bdring/TWANG32/TWANG32/SoundData.h

unsigned char PROGMEM sndStart[14444] = {
  0x52, 0x49, 0x46, 0x46, 0x64, 0x38, 0x00, 0x00, 0x57, 0x41, 0x56, 0x45,
  0x66, 0x6D, 0x74, 0x20, 0x10, 0x00, 0x00, 0x00, 0x01, 0x00, 0x01, 0x00,
  0x40, 0x1F, 0x00, 0x00, 0x40, 0x1F, 0x00, 0x00, 0x01, 0x00, 0x08, 0x00,
  0x64, 0x61, 0x74, 0x61, 0x40, 0x38, 0x00, 0x00, 0x80, 0x80, 0x80, 0x80,
  0x80, 0x7F, 0x80, 0x7F, 0x80, 0x80, 0x7F, 0x80, 0x7F, 0x80, 0x80, 0x7F,
  0x80, 0x7F, 0x80, 0x80, 0x7F, 0x80, 0x7F, 0x80, 0x7F, 0x80, 0x7F, 0x80,
  0x7F, 0x80, 0x7F, 0x80, 0x7F, 0x80, 0x7F, 0x80, 0x7F, 0x80, 0x80, 0x7F,
  0x80, 0x7F, 0x80, 0x80, 0x7F, 0x80, 0x7F, 0x80, 0x80, 0x7F, 0x80, 0x7F,
  0x80, 0x7F, 0x80, 0x80, 0x7F, 0x80, 0x7F, 0x80, 0x7F, 0x80, 0x80, 0x80,
  0x80, 0x80, 0x80, 0x80, 0x80, 0x7F, 0x7F, 0x7F, 0x7F, 0x7F, 0x7F, 0x7F,
  0x7F, 0x7F, 0x7F, 0x7F, 0x7F, 0x7F, 0x80, 0x7F, 0x80, 0x7F, 0x80, 0x80,
  0x80, 0x80, 0x80, 0x80, 0x80, 0x7F, 0x7F, 0x7F, 0x7F, 0x7F, 0x7F, 0x80,
  0x80, 0x80, 0x80, 0x80, 0x80, 0x80, 0x80, 0x80, 0x80, 0x80, 0x80, 0x80,
  0x80, 0x80, 0x80, 0x80, 0x80, 0x80, 0x7F, 0x80, 0x7F, 0x80, 0x7F, 0x80,
  0x80, 0x80, 0x80, 0x80, 0x80, 0x7F, 0x7F, 0x7F, 0x7F, 0x7F, 0x7F, 0x7F,
  0x7F, 0x7F, 0x7F, 0x7F, 0x7F, 0x7F, 0x7F, 0x7F, 0x7F, 0x7F, 0x7F, 0x7F,
  0x80, 0x7F, 0x80, 0x7F, 0x80, 0x7F, 0x7F, 0x7F, 0x7F, 0x7F, 0x7F, 0x80,
  0x80, 0x80, 0x80, 0x80, 0x80, 0x80, 0x80, 0x80, 0x80, 0x80, 0x80, 0x80,
  0x80, 0x80, 0x80, 0x80, 0x80, 0x80, 0x7F, 0x7F, 0x7F, 0x7F, 0x80, 0x80,
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
  0x88, 0x89, 0x89, 0x89, 0x8A, 0x8A, 0x8B, 0x8B, 0x8B, 0x8B, 0x8C, 0x8C,
  0x8D, 0x8D, 0x8E, 0x8D, 0x8E, 0x8E, 0x8F, 0x8F, 0x90, 0x8F, 0x91, 0x90,
  0x92, 0x90, 0x93, 0x90, 0x96, 0x7D, 0x69, 0x6F, 0x6C, 0x6F, 0x6E, 0x70,
  0x6F, 0x70, 0x70, 0x71, 0x71, 0x72, 0x72, 0x73, 0x73, 0x74, 0x73, 0x73,
  0x73, 0x74, 0x74, 0x74, 0x75, 0x75, 0x75, 0x76, 0x76, 0x77, 0x77, 0x78,
  0x78, 0x79, 0x79, 0x79, 0x7A, 0x7A, 0x7B, 0x7B, 0x7B, 0x7C, 0x7C, 0x7D,
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
};
